Ekstazaa/diy-audio-amp/input-stage/input_stage+vas_tb.asc

C1: cap; 470p
D1: diode; 1N914
D2: diode; 1N914
D3: diode; 1N914
D4: diode; 1N914
Q1: pnp; BC556B
Q2: pnp; BC556B
Q3: pnp; BC556B
Q4: npn; BC547B
Q5: pnp; BC556B
Q6: npn; BC547B
Q7: npn; BC547B
R1: res; 47k
R2: res; 200
R3: res; 330
R4: res; 330
R5: res; 100
Vdd: voltage; 24
Vi1: voltage; SINE(0 10 1k); AC 1
Vss: voltage; -24
Named nets: 0, vin, vout
;ac oct 1001 1 100G
.tran 0 20m 1m
.four 1k 10 -1 V(vout)
